kalak-io/electronic-dice/Firmware/types.h

#ifndef TYPES_H
#define	TYPES_H

typedef signed char     s8;
typedef signed short    s16;
typedef signed  long    s32;

typedef unsigned char   u8;
typedef unsigned short  u16;
typedef unsigned long   u32;

#endif	/* TYPES_H */
